oshwa/OHS2024Badge/hardware/OHS2024 Badge Release/OHS2024 Badge Release.kicad_sch

## KiCad design hardware/OHS2024 Badge Release/OHS2024 Badge Release.kicad_sch (2024-04-30)

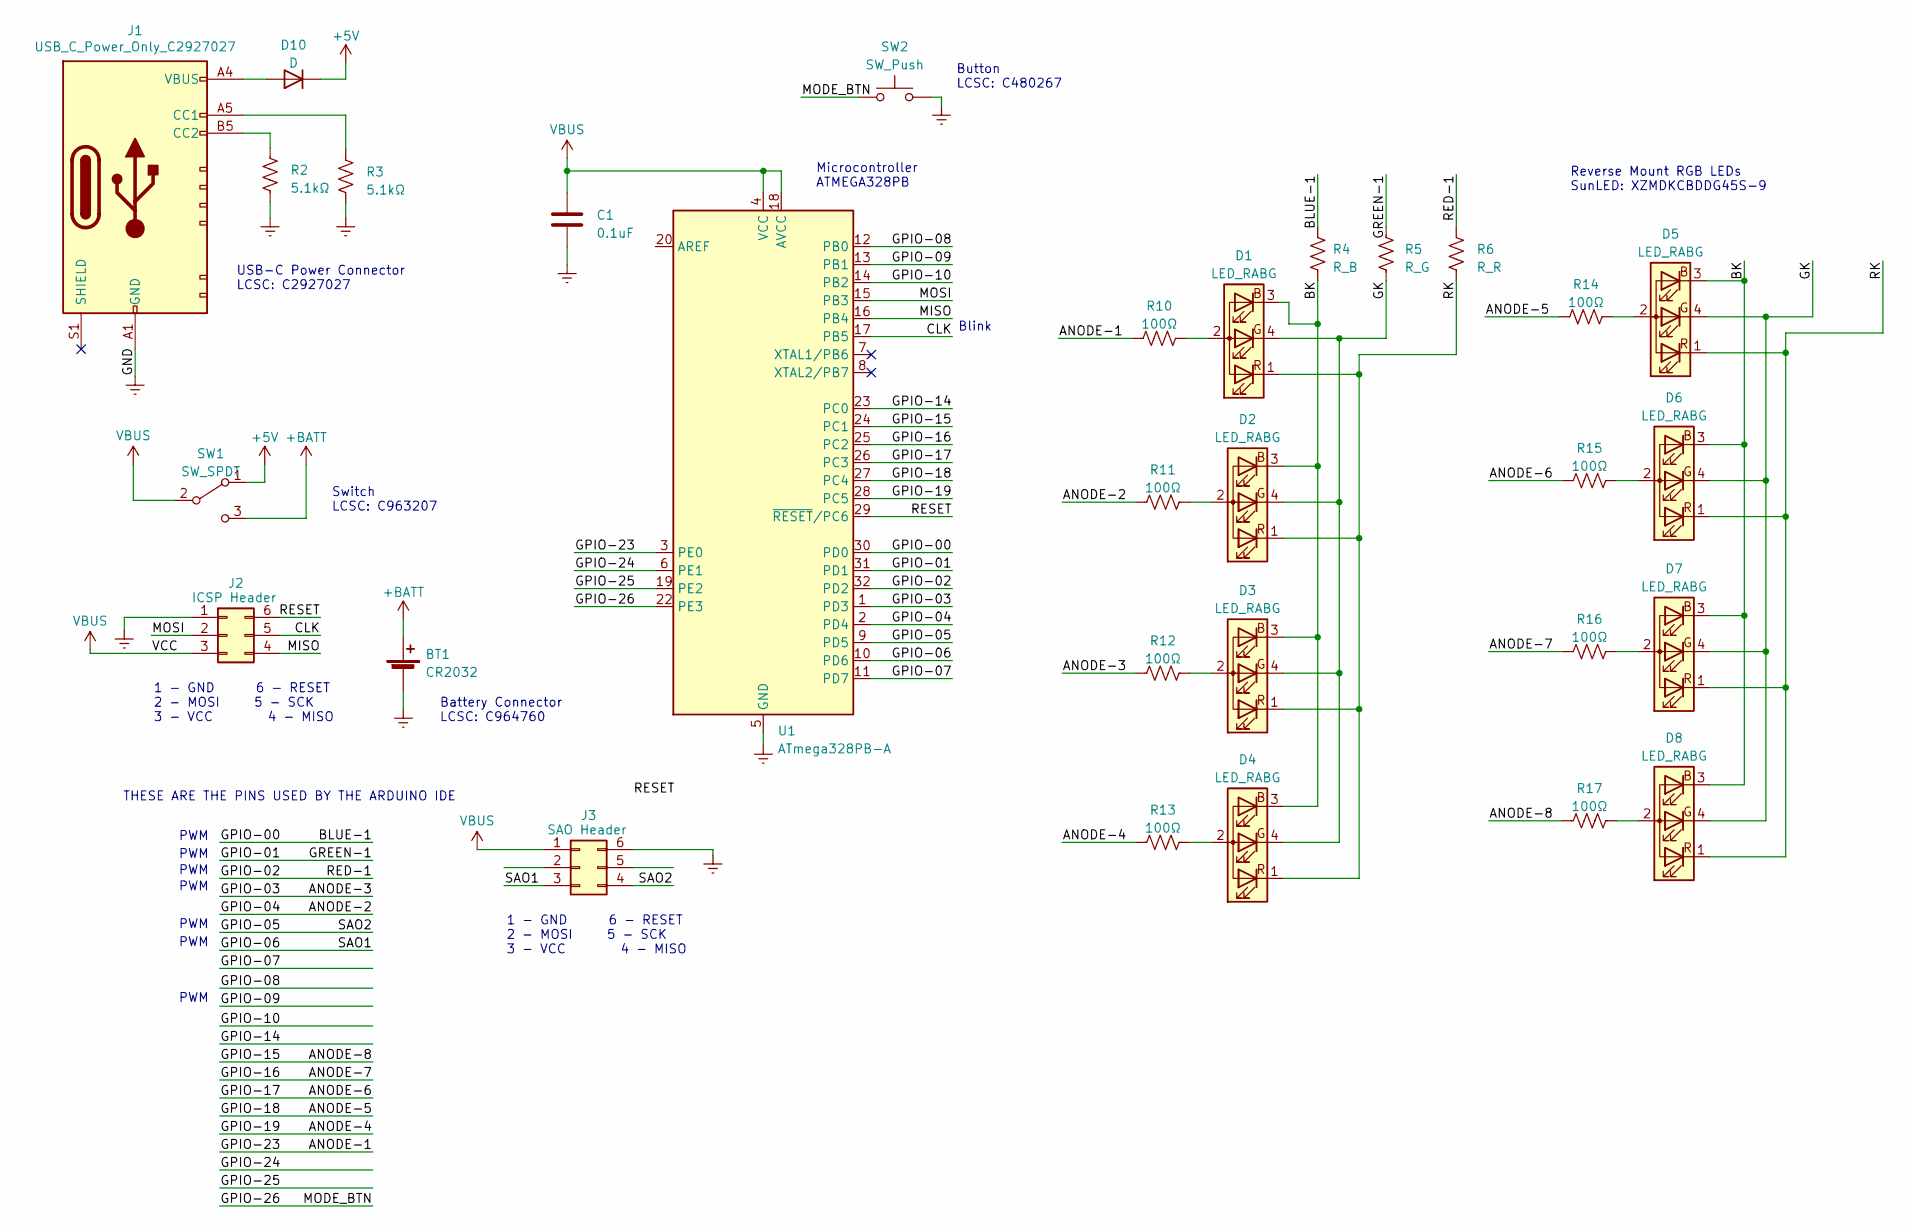
[picture p16: schematic OHS2024 Badge Release.kicad_sch]

Parts:
BT1: CR2032; BADGE - CR2032 HOLDER C964760
C1: 0.1uF; BADGE - C_0805
D1, D2, D3, D4, D5, D6, D7, D8: LED_RABG; BADGE - LED RGB Reverse XZMDKCBDDG45S-9
D10: D; BADGE - DO-214AC
J1: USB_C_Power_Only_C2927027; BADGE - USB C Power Only C2927027
J2: ICSP Header; Badge - ICSP Header (SMT)
J3: SAO Header; Badge - SAO Header
R2, R3: 5.1kΩ; BADGE - R_0805
R4: R_B; BADGE - R_0805
R5: R_G; BADGE - R_0805
R6: R_R; BADGE - R_0805
R10, R11, R12, R13, R14, R15, R16, R17: 100Ω; BADGE - R_0805
SW1: SW_SPDT; BADGE - SWITCH C963207
SW2: SW_Push; BADGE - BUTTON
U1: ATmega328PB-A; TQFP-32_7x7mm_P0.8mm

Connections:
+5V: D10.1 (K), SW1.1 (A)
+BATT: BT1.1 (+), SW1.3 (C)
ANODE-1: R10.2, U1.3 (PE0)
ANODE-2: R11.2, U1.2 (PD4)
ANODE-3: R12.2, U1.1 (PD3)
ANODE-4: R13.2, U1.28 (PC5)
ANODE-5: R14.2, U1.27 (PC4)
ANODE-6: R15.2, U1.26 (PC3)
ANODE-7: R16.2, U1.25 (PC2)
ANODE-8: R17.2, U1.24 (PC1)
BK: D1.3 (BK), D2.3 (BK), D3.3 (BK), D4.3 (BK), D5.3 (BK), D6.3 (BK), D7.3 (BK), D8.3 (BK), R4.1
BLUE-1: R4.2, U1.30 (PD0)
CLK: J2.5, U1.17 (PB5)
Earth: BT1.2 (-), C1.1, J1.A1 (GND), J1.A12 (GND), J1.B1 (GND), J1.B12 (GND), J2.1, J3.6, R2.2, R3.2, SW2.2, U1.5 (GND), U1.21 (GND)
GK: D1.4 (GK), D2.4 (GK), D3.4 (GK), D4.4 (GK), D5.4 (GK), D6.4 (GK), D7.4 (GK), D8.4 (GK), R5.1
GPIO-01: R5.2, U1.31 (PD1)
GPIO-02: R6.2, U1.32 (PD2)
GPIO-05: J3.4, U1.9 (PD5)
GPIO-06: J3.3, U1.10 (PD6)
GPIO-07: U1.11 (PD7)
GPIO-08: U1.12 (PB0)
GPIO-09: U1.13 (PB1)
GPIO-10: U1.14 (PB2)
GPIO-14: U1.23 (PC0)
GPIO-24: U1.6 (PE1)
GPIO-25: U1.19 (PE2)
GPIO-26: SW2.1, U1.22 (PE3)
MISO: J2.4, U1.16 (PB4)
MOSI: J2.2, U1.15 (PB3)
unnamed: D1.2 (A), R10.1
unnamed: D2.2 (A), R11.1
unnamed: D3.2 (A), R12.1
unnamed: D4.2 (A), R13.1
unnamed: D5.2 (A), R14.1
unnamed: D6.2 (A), R15.1
unnamed: D7.2 (A), R16.1
unnamed: D8.2 (A), R17.1
unnamed: D10.2 (A), J1.A4 (VBUS), J1.A9 (VBUS), J1.B4 (VBUS), J1.B9 (VBUS)
unnamed: J1.A5 (CC1), R3.1
unnamed: J1.B5 (CC2), R2.1
RESET: J2.6, U1.29 (~RESET/PC6)
RK: D1.1 (RK), D2.1 (RK), D3.1 (RK), D4.1 (RK), D5.1 (RK), D6.1 (RK), D7.1 (RK), D8.1 (RK), R6.1
VBUS: C1.2, J2.3, J3.1, SW1.2 (B), U1.4 (VCC), U1.18 (AVCC)

Notes on the sheet:
PWM
THESE ARE THE PINS USED BY THE ARDUINO IDE
Blink
Switch LCSC: C963207
Reverse Mount RGB LEDs SunLED: XZMDKCBDDG45S-9
USB-C Power Connector LCSC: C2927027
1 - GND 6 - RESET 2 - MOSI 5 - SCK 3 - VCC 4 - MISO
Microcontroller ATMEGA328PB
Battery Connector LCSC: C964760
Button LCSC: C480267
